geoffdavis/3DPrinterConfig/voronica/CANBUS/SB2040/H0a4bb9aa91b341e5a25d1acb4156db0cP.webp

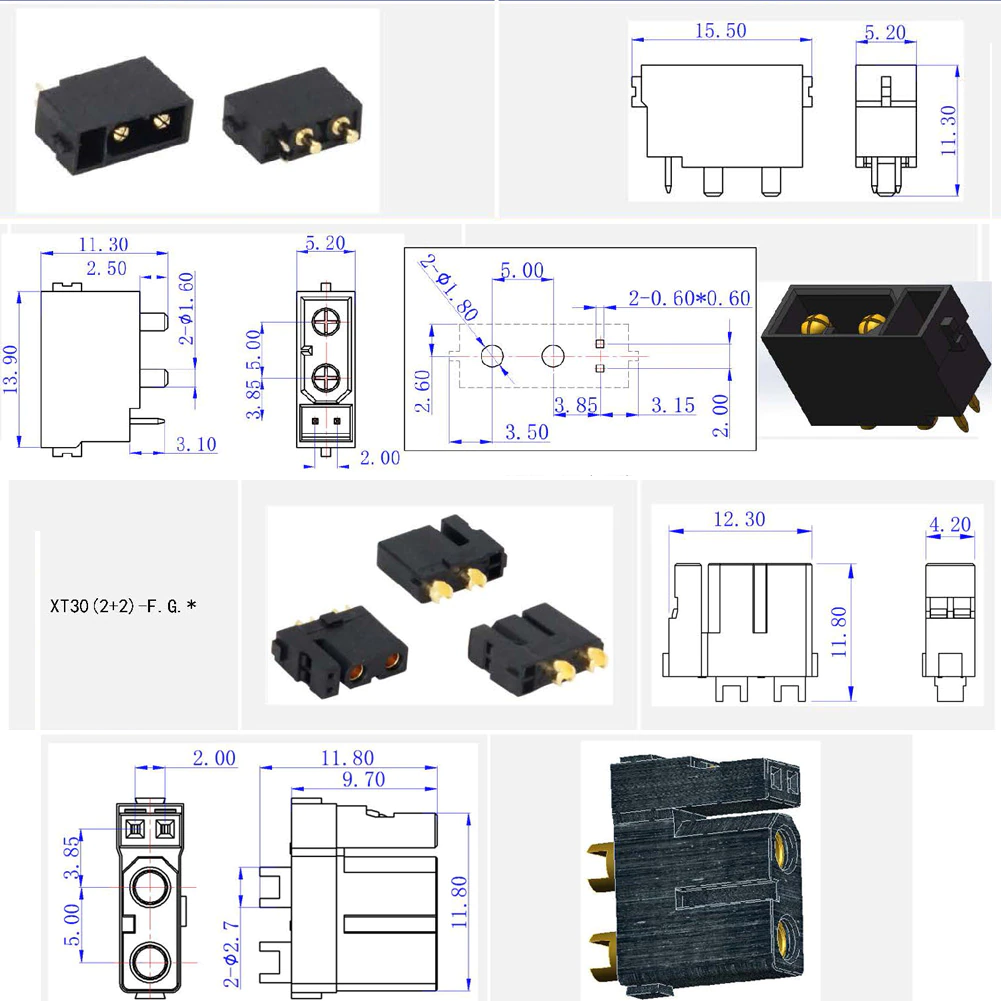
voronica/CANBUS/SB2040/H0a4bb9aa91b341e5a25d1acb4156db0cP.webp
