geoffdavis/3DPrinterConfig/voronica/CANBUS/SB2040/Hcbaf34d7871c420ca07bb667928e01d23.webp

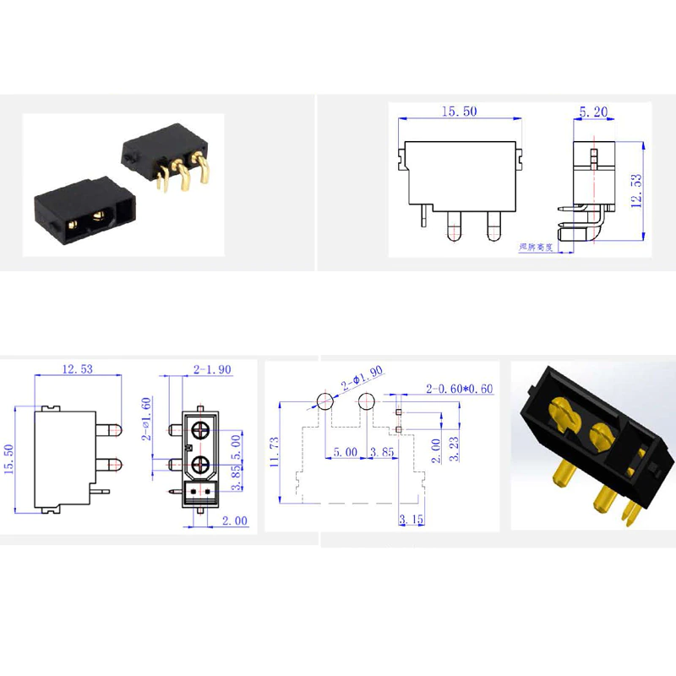
voronica/CANBUS/SB2040/Hcbaf34d7871c420ca07bb667928e01d23.webp
