geoffdavis/3DPrinterConfig/voronica/docs/Stepper Motors/Wiring_4_lead_Wires_c08b9b2bf8.png

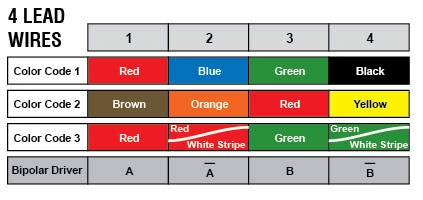
voronica/docs/Stepper Motors/Wiring_4_lead_Wires_c08b9b2bf8.png
