geoffdavis/3DPrinterConfig/smurf/klipper/printer.cfg

### UI
[include fluidd.cfg]

[mcu]
serial: /dev/serial0  # If you are using internal RPI serial port
# serial: /dev/ttyACM0 # If you are using RPI via USB connection to printer
restart_method: command

### CONTROL BOARD
[include config/boards/btt-skr-pico.cfg]

### RPI MCU
[include config/boards/rpi.cfg]

### Base Setup
[include config/printers/mpmd/mpmd.cfg]

### Stepper motors, drivers, & speed limits
[include config/printers/mpmd/steppers.cfg]

[include config/printers/mpmd/tmc2209.cfg]

[include config/printers/mpmd/speed-limits-basic.cfg]

# Stealth mode
# Note: this will make your printer quieter but less accurate, it's an inherent side effect of stealthchop
[include config/printers/mpmd/tmc2209-stealth.cfg]

### Homing
[include config/z-probe/probe.cfg]

#[include config/sensorless-homing.cfg]
[include config/printers/mpmd/endstops.cfg]

### Toolhead
# Extruder
[include config/extruders/cr10-clone.cfg]
[include config/sensors/btt-smartie.cfg]

# Hotend
[include config/hotends/revo.cfg]

### Macros
[include config/macros.cfg]
[include config/cancel-object.cfg]
[include config/chassis-neopixel.cfg]

[include config/beeper.cfg]

### SAVE VARIABLES
[save_variables]
filename: ~/klipper_config/saved_vars.cfg

### Local overrides

[printer]
#delta_radius: 62.7

[stepper_a]
#angle: 212.000000
#position_endstop: 120
#arm_length: 121.36

[stepper_b]
#angle: 330.000000
#position_endstop: 120
#arm_length: 121.36

[stepper_c]
#angle: 90.000000
#position_endstop: 120
#arm_length: 121.36

#[endstop_phase]

[probe]
#z_offset: -0.554

#*# <---------------------- SAVE_CONFIG ---------------------->
#*# DO NOT EDIT THIS BLOCK OR BELOW. The contents are auto-generated.
#*#
#*# [extruder]
#*# control = pid
#*# pid_kp = 29.404
#*# pid_ki = 3.770
#*# pid_kd = 57.337
#*#
#*# [probe]
#*# z_offset = -0.304
#*#
#*# [printer]
#*# delta_radius = 69.265389
#*#
#*# [stepper_a]
#*# angle = 208.082418
#*# arm_length = 129.677009
#*# position_endstop = 129.212455
#*#
#*# [stepper_b]
#*# angle = 329.908835
#*# arm_length = 134.705170
#*# position_endstop = 126.945224
#*#
#*# [stepper_c]
#*# angle = 90.000000
#*# arm_length = 131.403512
#*# position_endstop = 127.320085
#*#
#*# [delta_calibrate]
#*# height0 = 0.0
#*# height0_pos = 12766.000,12830.000,12696.000
#*# height1 = 0.0
#*# height1_pos = 15735.000,15881.000,10928.000
#*# height2 = 0.0
#*# height2_pos = 12413.000,17949.000,12333.000
#*# height3 = 0.0
#*# height3_pos = 11097.000,15438.000,15205.000
#*# height4 = 0.0
#*# height4_pos = 12305.000,12376.000,16029.000
#*# height5 = 0.0
#*# height5_pos = 14803.000,11220.000,14765.000
#*# height6 = 0.0
#*# height6_pos = 16615.000,12211.000,12109.000
#*# distance0 = 42.71
#*# distance0_pos1 = 12720.683,12836.172,12800.936
#*# distance0_pos2 = 11138.046,15373.365,15327.350
#*# distance1 = 42.51
#*# distance1_pos1 = 12813.143,12654.730,12892.586
#*# distance1_pos2 = 12453.914,12277.408,17382.719
#*# distance2 = 42.019999999999996
#*# distance2_pos1 = 12996.640,12564.830,12800.936
#*# distance2_pos2 = 15602.015,10997.053,15327.350
#*# distance3 = 42.52
#*# distance3_pos1 = 13087.652,12654.234,12619.827
#*# distance3_pos2 = 17680.406,12270.001,12239.706
#*# distance4 = 42.21
#*# distance4_pos1 = 12992.919,12835.668,12530.334
#*# distance4_pos2 = 15527.374,15363.343,10964.985
#*# distance5 = 43.43000000000001
#*# distance5_pos1 = 12809.483,12927.741,12619.827
#*# distance5_pos2 = 12399.234,17431.969,12239.706
#*# distance6 = 42.64
#*# distance6_pos1 = 11231.120,14818.516,15112.508
#*# distance6_pos2 = 12576.568,12137.110,17139.114
#*# distance7 = 42.25
#*# distance7_pos1 = 12553.959,12116.767,16675.793
#*# distance7_pos2 = 15645.929,11027.004,15025.022
#*# distance8 = 42.26
#*# distance8_pos1 = 15376.827,11087.549,14774.700
#*# distance8_pos2 = 17424.591,12391.071,12099.921
#*# distance9 = 42.44
#*# distance9_pos1 = 16945.852,12370.772,12079.853
#*# distance9_pos2 = 15219.829,15408.928,10995.112
#*# distance10 = 42.589999999999996
#*# distance10_pos1 = 14967.704,15148.609,11055.574
#*# distance10_pos2 = 12259.859,17187.540,12360.610
#*# distance11 = 42.730000000000004
#*# distance11_pos1 = 12241.335,16722.072,12340.098
#*# distance11_pos2 = 11170.063,15069.973,15372.496
