geoffdavis/3DPrinterConfig/voronica/klipper/trad_rack/trad_rack_btt_skr_mini_e3_v2.cfg

[mcu tr]
serial: /dev/serial/by-id/usb-Klipper_stm32f103xe_30FFDA054E4E353717730551-if00
restart_method: command

[temperature_sensor TradRack]
sensor_type: temperature_mcu
sensor_mcu: tr
min_temp: 0
max_temp: 125

[trad_rack]
selector_max_velocity: 400
selector_max_accel: 10000
toolhead_fil_sensor_pin: ^!sb2040:gpio29
lane_count: 14
lane_spacing: 17.0
servo_down_angle: 0.0
servo_up_angle: 131.0
toolhead_unload_speed: 20
extruder_load_speed: 20
toolhead_sense_speed: 20
selector_unload_length: 17.5
bowden_length: 950.0
extruder_load_length: 44.5
hotend_load_length: 6.0
toolhead_unload_length: 40.0
buffer_pull_speed: 200.0    # increase this to 300+ once you are ready
                            # (but some motors may not be able to handle this).
sync_to_extruder: true

[stepper_tr_selector]
# connected to XM
step_pin: tr:PB13
dir_pin: !tr:PB12
enable_pin: !tr:PB14
rotation_distance: 40
microsteps: 16
full_steps_per_rotation: 200
endstop_pin: ^tr:PC0 # X-STOP
position_min: 0.0
position_endstop: 0.0
position_max: 221   # (lane_count - 1) * lane_spacing
homing_speed: 30

[stepper_tr_fil_driver]
# connected to EM
step_pin: tr:PB3
dir_pin: !tr:PB4
enable_pin: !tr:PD2
rotation_distance: 22.67895
gear_ratio: 50:17
microsteps: 16
full_steps_per_rotation: 200
endstop_pin: ^tr:PC2  # selector filament sensor, Z-STOP
position_min: -5000
position_endstop: 0
position_max: 5000
homing_positive_dir: False

[tmc2209 stepper_tr_selector]
# connected to XM
uart_pin: tr:MMU_TMC_UART
tx_pin: tr:PC10
uart_address: 0
interpolate: True
run_current: 0.63   # for a 1A peak motor
sense_resistor: 0.110

[tmc2209 stepper_tr_fil_driver]
# connected to EM
uart_pin: tr:MMU_TMC_UART
tx_pin: tr:PC10
uart_address: 3
interpolate: False
run_current: 1.27   # for a 2A peak motor
sense_resistor: 0.110

[servo tr_servo]
# connected to servo/bltouch control pin
pin: tr:PA1
maximum_servo_angle: 131
minimum_pulse_width: 0.000700
maximum_pulse_width: 0.002200

[extruder]
max_extrude_only_distance: 200
max_extrude_cross_section: 100

# Macros
[gcode_macro ACTIVATE_EXTRUDER]
rename_existing: ACTIVATE_EXTRUDER.1
gcode:
    {% set EXTRUDER = params.EXTRUDER|default('extruder')|lower|replace('extruder', '') %}
    {% if EXTRUDER == '' %}
        {% set EXTRUDER = '0' %}
    {% endif %}
    TR_LOAD_TOOLHEAD LANE={EXTRUDER}
