geoffdavis/3DPrinterConfig/hodad/klipper/config/beeper.cfg

#####################################################################
#	Tones
# 
#     |~~~~~~~~~~~~~~~|
#     |~~~~~~~~~~~~~~~|
#     |               |
# /~~\|           /~~\|
# \__/            \__/
# 
#####################################################################

# Source: https://github.com/majarspeed/Profiles-Gcode-Macros/blob/main/Beeper%20tunes/tones.cfg

[gcode_macro TOGGLE_BEEPER]
description: Toggle the printer beeper on and off.
gcode:
	{% set beeper_state = printer.save_variables.variables.beeper_state|lower %}

	{% if printer['gcode_macro _USER_VARIABLE'].debug == 1 %}
		{action_respond_info('==== TOGGLE_BEEPER ====')}
		{action_respond_info("beeper_state: %s" % (beeper_state))}
		{action_respond_info('===============')}
	{% endif %}

	{% if beeper_state == "off" %}
		{action_respond_info('beeper is off, turning it on')}
		SAVE_VARIABLE VARIABLE=beeper_state VALUE='"on"'
	{% else %}
		{action_respond_info('beeper is on= turning it off')}
		SAVE_VARIABLE VARIABLE=beeper_state VALUE='"off"'
	{% endif %}
	SONG_SINGLE_BEEP

[gcode_macro SONG_SINGLE_BEEP]
gcode:
	M300 S830.61 P137

[gcode_macro BEEP]
gcode:
    # Parameters
    {% set i = params.I|default(1)|int %}           ; Iterations (number of times to beep).
    {% set dur = params.DUR|default(100)|int %}     ; Duration/wait of each beep in ms. Default 100ms.
    {% set freq = params.FREQ|default(2000)|int%}   ; Frequency in Hz. Default 2kHz.

    {% for iteration in range(1|int) %}
        SET_PIN PIN=beeper VALUE=0.8 CYCLE_TIME={ 1.0/freq if freq >0 else 1 }
        G4 P{dur}
        SET_PIN PIN=beeper VALUE=0
        G4 P{dur}
    {% endfor %}

[gcode_macro M300]
gcode:
	{% set S = params.S|default(1000)|int %}
	{% set P = params.P|default(100)|int %}

		SET_PIN PIN=beeper VALUE=0.5 CYCLE_TIME={ 1.0/S if S > 0 else 1 }
		G4 P{P}
		SET_PIN PIN=beeper VALUE=0

[gcode_macro SONG_THUNDERSTRUCK]
gcode:
	M300 S987 P166
	M300 S2489 P166
	M300 S987 P166
	M300 S2959 P166
	M300 S987 P166
	M300 S2489 P166
	M300 S987 P166
	M300 S2959 P166
	M300 S987 P166
	M300 S2489 P166
	M300 S987 P166
	M300 S2959 P166
	M300 S987 P166
	M300 S2959 P166
	M300 S987 P166
	M300 S2959 P166
	M300 S2637 P166
	M300 S987 P166
	M300 S1760 P166
	M300 S987 P166
	M300 S2637 P166
	M300 S987 P166
	M300 S1760 P166
	M300 S987 P166
	M300 S2637 P166
	M300 S987 P166
	M300 S1760 P166
	M300 S987 P166
	M300 S2637 P166
	M300 S987 P166
	M300 S1760 P166

[gcode_macro SONG_AFRICA]
gcode:
	M300 S2959 P150
	M300 S2959 P150
	M300 S2959 P150
	M300 S2959 P450
	M300 S2959 P150
	M300 S2959 P450
	M300 S3322 P300
	M300 S1864 P150
	M300 S1975 P1200
	M300 S2489 P150
	M300 S2489 P450
	M300 S2637 P300
	M300 S2959 P300
	M300 S2959 P300
	M300 S2637 P225
	M300 S2637 P300
	M300 S2489 P300
	M300 S2217 P600
	M300 S2217 P300
	M300 S987 P300
	M300 S2489 P600
	M300 S2217 P150
	M300 S987 P300
	M300 S2217 P1200
	M300 S2959 P150
	M300 S2959 P150
	M300 S2959 P600
	M300 S2959 P150
	M300 S2959 P450
	M300 S3322 P300
	M300 S1864 P150
	M300 S1975 P1200
	M300 S2489 P150
	M300 S2489 P150
	M300 S2489 P150
	M300 S2637 P300
	M300 S2959 P300
	M300 S2959 P450
	M300 S2637 P300
	M300 S2637 P300
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

[gcode_macro SONG_STARWARS_IMP]
gcode:
	M300 S1174 P401
	M300 S1174 P401
	M300 S1174 P401
	M300 S466 P267
	M300 S1396 P133
	M300 S1174 P401
	M300 S466 P267
	M300 S1396 P133
	M300 S1174 P803

[gcode_macro SONG_ALLIWANT]
gcode:
	M300 S1046 P333
	M300 S1318 P333
	M300 S1567 P333
	M300 S987 P166
	M300 S0 P41
	M300 S2093 P333
	M300 S0 P83
	M300 S0 P41
	M300 S987 P333
	M300 S880 P166
	M300 S0 P41
	M300 S1567 P333
	M300 S0 P83
	M300 S0 P41
	M300 S2349 P333
	M300 S2093 P333
	M300 S2093 P333
	M300 S987 P333
	M300 S2093 P166
	M300 S0 P41
	M300 S987 P333
	M300 S0 P83
	M300 S0 P41
	M300 S880 P166
	M300 S1567 P333
	M300 S0 P166
	M300 S1396 P333
	M300 S880 P333
	M300 S2093 P333
	M300 S2349 P333
	M300 S2637 P333
	M300 S2349 P166
	M300 S2093 P333
	M300 S880 P333
	M300 S0 P166
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
	M300 P249 S262
	M300 P249 S784
	M300 P247 S698
	M300 P247 S659
	M300 P250 S587
	M300 P265 S587
	M300 P248 S659
	M300 P247 S698
	M300 P249 S262
	M300 P249 S698
	M300 P247 S262
	M300 P247 S784
	M300 P250 S880
	M300 P265 S932
	M300 P248 S932
	M300 P247 S880
	M300 P249 S349
	M300 P249 S784
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
