geoffdavis/3DPrinterConfig/voronica/klipper/macros/start_stop.cfg

; Start/stop macros
; Uses heatsoak.cfg

[gcode_macro _START_STOP_VARS]
variable_trad_rack_present: 1
gcode:

[gcode_macro PRINT_START]
gcode:
    # Parameters
    {% set bedtemp = params.BED|default(60)|int %}
    {% set hotendtemp = params.HOTEND|default(215)|int %}
    {% set chambertemp = params.CHAMBER|default(0)|int %}
    {% set force_bedmesh = params.BEDMESH|default(1)|int %}
    {% set force_qgl = params.FORCE_QGL|default(1)|int %}


    {% set COLORS = params.COLORS|default("")|string %}
    {% set colors = COLORS.split(",") %}
    {% set ttg_map = printer.mmu.ttg_map %}

    #SET_FILAMENT_SENSOR SENSOR=btt_smartie ENABLE=0                          ; disable filament sensor

    {% if printer["temperature_sensor chamber"].temperature < chambertemp %}
      RESPOND MSG="Chamber Heating"
		  _HEATSOAK TEMP={bedtemp} MOVE=1                    # Set up to heat soak if chamber temp is set higher than current reading
		  M190 S{bedtemp}                                    # Set target bed temp & wait for it
      RESPOND MSG="Waiting for Chamber Temperature to reach {chambertemp}C"
      TEMPERATURE_WAIT SENSOR="temperature_sensor chamber" MINIMUM={chambertemp}   # Do the actual heat soak wait, until chamber temp is at target
      RESPOND MSG="Chamber Temperature reached {chambertemp}C"
    {% else %}
      RESPOND MSG="Bed Heating"
        {% if printer.heater_bed.temperature < (bedtemp-2) %}
          _HEATSOAK TEMP={bedtemp} MOVE=1	        	 # Bed is below target temp, get it heating & safely park toolhead
          M190 S{bedtemp}                                # Set bed target temp & wait for it
        {% else %}
          _HEATSOAK TEMP={bedtemp} MOVE=0                # Just do a bed heat, no champer temp (open case for PLA)
        {% endif %}
    {% endif %}
    M106 S0                                                  # Turn off part cooling fan from heatsoak

    # Conditionally re-mesh the bed
    {% if force_gql or not printer.quad_gantry_level.applied %}
      RESPOND MSG="Running Z-Gantry Leveling and Bed Meshing"
      led_meshing
      BED_MESH_CLEAR                                           # Clear old bed mesh  
      CALIBRATE_Z
      BED_MESH_CALIBRATE ADAPTIVE=1 ADAPTIVE_MARGIN=5
      LED_STANDBY
    {% elif force_bedmesh %}
      RESPOND MSG="Running Bed Meshing"
      led_meshing
      BED_MESH_CLEAR  
      BED_MESH_CALIBRATE ADAPTIVE=1 ADAPTIVE_MARGIN=5
      LED_STANDBY
    {% else %}
      RESPOND MSG="Skipping Bed Meshing"
      G28 ; Home all axes
    {% endif %}

    LED_HEATING
    #G1 X175 Y0 Z20         # Move tool head to safe distance from bed

    RESPOND MSG="Heating nozzle"
    M106 S205 ; set fan speed
    M109 S{hotendtemp}                                       # Do final nozzle heat
 
    LED_PRINTING                                             # Prep done, start print
    RESPOND MSG="Printing"
    SONG_SINGLE_BEEP

    #VORON_PURGE
    G90                            ; absolute positioning
    G1 Z20 F3000                   ; move nozzle away from bed 

#   Use PRINT_END for the slicer ending script - please customise for your slicer of choice
[gcode_macro PRINT_END]
gcode:
  {% set xy_offset = 20 %}
  {% set filter_off = 300 %}
  {% set retract_dist = 1800 %}
  {% set travel = 20000 %}
  {% set filter_off = 300 %}
  # calculate safe move
  {% set max = printer.toolhead.axis_maximum %}
  {% set act = printer.toolhead.position %}
  {% set safe = {'x': 20.0 if act.x|float < (max.x|float - 20.0) else -20.0,
                 'y': 20.0 if act.y|float < (max.y|float - 20.0) else -20.0,
                 'z':  2.0 if act.z|float < (max.z|float -  2.0) else (max.z|float - act.z|float)} %}
  
  M400                           ; wait for buffer to clear
  #SET_FILAMENT_SENSOR SENSOR=btt_smartie ENABLE=0                          ; disable filament sensor
  {% if printer.mmu is not defined or ( printer.mmu is defined and printer.mmu.enabled ) %}
  G92 E0                         ; zero the extruder
  G1 E-5 F{retract_dist}                ; retract filament
  G91                            ; relative positioning
  G0 Z1.00 X{safe.x} Y{safe.y} Z{safe.z} F{travel}    ; move nozzle to remove stringing
  {% endif %}

  TURN_OFF_HEATERS
  M107                           ; turn off fan
  G90                            ; absolute positioning
  PARKREAR            ; park nozzle at rear
  UPDATE_DELAYED_GCODE ID=_DELAY_FILTER_OFF DURATION={filter_off}
  ;BED_MESH_CLEAR
  ;Song_Simpsons
  M117 Print Complete!
  UPDATE_DELAYED_GCODE ID=clear_display DURATION=10
  LED_STANDBY
  M220 S100 ; set feedrate percentage back to default
  M221 S100 ; set speed percentage back to default
