geoffdavis/3DPrinterConfig/voronica/klipper/pause_resume.cfg

# Pause / Resume
# https://ellis3dp.com/Print-Tuning-Guide/articles/useful_macros/pause_resume_filament.html


# Declare the pause_resume feature
[pause_resume]

[gcode_macro PAUSE_RESUME_VARS]
variable_manage_sensor: 0 ; set this to 0 if btt-smartie is commented out
variable_sensor_name: "btt_smartie"
gcode:

[gcode_macro PAUSE]
rename_existing: BASE_PAUSE
gcode:
    # Parameters
    {% set z = params.Z|default(10)|int %}                                               ; z hop amount

    {% if printer['pause_resume'].is_paused|int == 0 %}
        SET_GCODE_VARIABLE MACRO=RESUME VARIABLE=zhop VALUE={z}                              ; set z hop variable for reference in resume macro
        SET_GCODE_VARIABLE MACRO=RESUME VARIABLE=etemp VALUE={printer['extruder'].target}    ; set hotend temp variable for reference in resume macro

        {% if printer['gcode_macro PAUSE_RESUME_VARS'].manage_sensor > 0 %}
        SET_FILAMENT_SENSOR SENSOR={printer['gcode_macro PAUSE_RESUME_VARS'].sensor_name} ENABLE=0                                  ; disable filament sensor
        {% endif %}
        SAVE_GCODE_STATE NAME=PAUSE                                                          ; save current print position for resume
        LED_STANDBY                                                                          ; Set lights for standby mode
        BASE_PAUSE                                                                           ; pause print
        {% if (printer.gcode_move.position.z + z) < printer.toolhead.axis_maximum.z %}       ; check that zhop doesn't exceed z max
            G91                                                                              ; relative positioning
            G1 Z{z} F900                                                                     ; raise Z up by z hop amount
        {% else %}
            { action_respond_info("Pause zhop exceeds maximum Z height.") }                  ; if z max is exceeded, show message and set zhop value for resume to 0
            SET_GCODE_VARIABLE MACRO=RESUME VARIABLE=zhop VALUE=0
        {% endif %}
        G90                                                                                  ; absolute positioning
        G1 X{printer.toolhead.axis_maximum.x/2} Y{printer.toolhead.axis_minimum.y+5} F6000   ; park toolhead at front center
        SAVE_GCODE_STATE NAME=PAUSEPARK                                                      ; save parked position in case toolhead is moved during the pause (otherwise the return zhop can error)
        ;M104 S0                                                                              ; turn off hotend (disabled because it breaks tradrack)
        SET_IDLE_TIMEOUT TIMEOUT=43200                                                       ; set timeout to 12 hours
    {% endif %}

[gcode_macro RESUME]
rename_existing: BASE_RESUME
variable_zhop: 0
variable_etemp: 0
gcode:
    # Parameters
    {% set e = params.E|default(2.5)|int %}                                          ; hotend prime amount (in mm)

    {% if printer['pause_resume'].is_paused|int == 1 %}
        
        {% if printer['gcode_macro PAUSE_RESUME_VARS'].manage_sensor > 0 %}
        SET_FILAMENT_SENSOR SENSOR={printer['gcode_macro PAUSE_RESUME_VARS'].sensor_name} ENABLE=1                          ; enable filament sensor
        {% endif %}
        LED_PRINTING                                                                    ; reset LCD color
        SET_IDLE_TIMEOUT TIMEOUT={printer.configfile.settings.idle_timeout.timeout}  ; set timeout back to configured value
        {% if etemp > 0 %}
            M109 S{etemp|int}                                                        ; wait for hotend to heat back up
        {% endif %}
        RESTORE_GCODE_STATE NAME=PAUSEPARK MOVE=1 MOVE_SPEED=100                     ; go back to parked position in case toolhead was moved during pause (otherwise the return zhop can error)
        G91                                                                          ; relative positioning
        M83                                                                          ; relative extruder positioning
        {% if printer[printer.toolhead.extruder].temperature >= printer.configfile.settings.extruder.min_extrude_temp %}
            G1 Z{zhop * -1} E{e} F900                                                ; prime nozzle by E, lower Z back down
        {% else %}
            G1 Z{zhop * -1} F900                                                     ; lower Z back down without priming (just in case we are testing the macro with cold hotend)
        {% endif %}
        RESTORE_GCODE_STATE NAME=PAUSE MOVE=1 MOVE_SPEED=60                          ; restore position
        BASE_RESUME                                                                  ; resume print
    {% endif %}

[gcode_macro CANCEL_PRINT]
rename_existing: BASE_CANCEL_PRINT
gcode:
    SET_IDLE_TIMEOUT TIMEOUT={printer.configfile.settings.idle_timeout.timeout} ; set timeout back to configured value
    CLEAR_PAUSE
    SDCARD_RESET_FILE
    PRINT_END
    BASE_CANCEL_PRINT

[delayed_gcode DISABLEFILAMENTSENSOR]
initial_duration: 1
gcode:
    {% if printer['gcode_macro PAUSE_RESUME_VARS'].manage_sensor > 0 %} 
    SET_FILAMENT_SENSOR SENSOR={printer['gcode_macro PAUSE_RESUME_VARS'].sensor_name} ENABLE=0
    {% endif %}
