geoffdavis/3DPrinterConfig/voronica/klipper/fluidd.cfg

[virtual_sdcard]
path: /home/pi/printer_data/gcodes

[pause_resume]

[display_status]

[gcode_macro CANCEL_PRINT]
description: Cancel the actual running print
rename_existing: CANCEL_PRINT_BASE
gcode:
    TURN_OFF_HEATERS
    CANCEL_PRINT_BASE

# See macros/pause_resume.cfg for PAUSE and RESUME macros
