geoffdavis/3DPrinterConfig/voronica/klipper/macros/M141.cfg

# Set exhaust fan temperature target
[gcode_macro M141]
gcode:
    #SET_TEMPERATURE_FAN_TARGET TEMPERATURE_FAN=exhaust_fan TARGET={params.S}
    RESPOND MSG="M141: exhaust fan is a heater_fan, no direct control available"
