geoffdavis/3DPrinterConfig/voronica/klipper/probe.cfg

#####################################################################
#   Probe
#####################################################################

##  This probe is not used for Z height, only Quad Gantry Leveling
##  In Z+ position
[probe]
##  If your probe is NO instead of NC, change pin to ^!PA3
#pin: ^Z_MIN
pin: !sb2040:gpio28
x_offset: 0
#y_offset: 25.0 # physical probe
y_offset: 0 # TAP
#z_offset: -1.000
speed: 10.0
samples: 3
samples_result: median
sample_retract_dist: 3.0
samples_tolerance: 0.006
samples_tolerance_retries: 3

activate_gcode:
    {% set PROBE_TEMP = 170 %}
    {% set MAX_TEMP = PROBE_TEMP + 5 %}
    {% set ACTUAL_TEMP = printer.extruder.temperature %}
    {% set TARGET_TEMP = printer.extruder.target %}

    {% if TARGET_TEMP > PROBE_TEMP %}
        { action_respond_info('Extruder temperature target of %.1fC is too high, lowering to %.1fC' % (TARGET_TEMP, PROBE_TEMP)) }
        M109 S{ PROBE_TEMP }
    {% else %}
        # Temperature target is already low enough, but nozzle may still be too hot.
        {% if ACTUAL_TEMP > MAX_TEMP %}
            { action_respond_info('Extruder temperature %.1fC is still too high, waiting until below %.1fC' % (ACTUAL_TEMP, MAX_TEMP)) }
            TEMPERATURE_WAIT SENSOR=extruder MAXIMUM={ MAX_TEMP }
        {% endif %}
    {% endif %}

[bed_mesh]
#speed: 300
speed: 1000
#horizontal_move_z: 10
horizontal_move_z: 3
mesh_min: 40, 40
mesh_max: 310,310
#fade_start: 0.6
fade_start: 0.8
fade_end: 10.0
probe_count: 5,5
algorithm: bicubic
#relative_reference_index: 12
zero_reference_position: 175.0, 175.0

##  Use QUAD_GANTRY_LEVEL to level a gantry.
##  Min & Max gantry corners - measure from nozzle at MIN (0,0) and 
##  MAX (250, 250), (300,300), or (350,350) depending on your printer size
##  to respective belt positions
[quad_gantry_level]

#--------------------------------------------------------------------
##  Gantry Corners for 250mm Build
##  Uncomment for 250mm build
#gantry_corners:
#   -60,-10
#   310, 320
##  Probe points
#points:
#   50,25
#   50,175
#   200,175
#   200,25
    
##  Gantry Corners for 300mm Build
##  Uncomment for 300mm build
#gantry_corners:
#   -60,-10
#   360,370
##  Probe points
#points:
#   50,25
#   50,225
#   250,225
#   250,25

##  Gantry Corners for 350mm Build
##  Uncomment for 350mm build
gantry_corners:
   -60,-10
   410,420
##  Probe points
points:
   50,25
   50,275
   300,275
   300,25

#--------------------------------------------------------------------
#speed: 150
speed: 1000
horizontal_move_z: 10
retries: 8
retry_tolerance: 0.0075
max_adjust: 10
