geoffdavis/3DPrinterConfig/voronica/klipper/macros/heatsoak.cfg

[gcode_macro _HEATSOAK]
description: Helper: Set up to heat soak printer. Usage: _HEATSOAK [TEMP=temp(110)] [MOVE=move(1)]
gcode:
    {% set temp = params.TEMP|default(110)|int %}
    {% set move = params.MOVE|default(1)|int %}
	
    LED_HEATING
    RESPOND MSG="Warming up"
	M141 S0                                                 # Turn off exhaust fan
	M140 S{temp}                                            # Heat the bed
  M104 S170                                               # Set hotend to no-ooze temp
	{% if temp >= 90 %}                                    # It's ABS or other high-temp plastic, closed case
		M106 S205                                             # Turn on part fan to 80% for 
		_FILTER_ON                                            # Turn on Nevermore fans to circulate & accelerate chamber soak
    _FILTER_INFO
	{% else %}
		M106 S0                                               # Turn off part fan. Open case, no need
		_SET_FILTER                                           # Make sure Nevermore is off
    _FILTER_INFO
	{% endif %}
	
	{% if move == 1 %}
		_CG28                                                 # Conditional home
		PARKCENTER                                            # Park toolhead in safe location (center volume)
		LED_HEATING
	{% endif %}
