geoffdavis/3DPrinterConfig/hodad/klipper/klipper-expander.cfg

[mcu expander]
serial: /dev/serial/by-id/usb-Klipper_stm32f042x6_08002300134330534E373720-if00
restart_method: command

[output_pin caselight]
pin: expander:PA0
pwm: true
shutdown_value: 0
value: 1
cycle_time: 0.01

[neopixel expander]
pin: expander:PB1
chain_count: 1
initial_RED: 0.9
initial_GREEN: 0.3
initial_BLUE: 0.0
