geoffdavis/3DPrinterConfig/hodad/klipper/V0Display.cfg

[mcu display]
serial: /dev/serial/by-id/usb-Klipper_stm32f042x6_05001A000643564E32313720-if00
restart_method: command

[display]
lcd_type: sh1106
i2c_mcu: display
i2c_bus: i2c1a
# Set the direction of the encoder wheel
#   Standard: Right (clockwise) scrolls down or increases values. Left (counter-clockwise scrolls up or decreases values.
encoder_pins: ^display:PA3, ^display:PA4
#   Reversed: Right (clockwise) scrolls up or decreases values. Left (counter-clockwise scrolls down or increases values.
#encoder_pins: ^display:PA4, ^display:PA3
click_pin: ^!display:PA1
kill_pin: ^!display:PA5
x_offset: 2
#   Use X offset to shift the display towards the right. Value can be 0 to 3
vcomh: 31
#   Set the Vcomh value on SSD1306/SH1106 displays. This value is
#   associated with a "smearing" effect on some OLED displays. The
#   value may range from 0 to 63. Default is 0.
#   Adjust this value if you get some vertical stripes on your display. (31 seems to be a good value)

[neopixel displayStatus]
pin: display:PA0
chain_count: 1
color_order: GRB
initial_RED: 0.2
initial_GREEN: 0.05
initial_BLUE: 0

[output_pin beeper]
pin: display:PA6 # gpio1
value: 0
shutdown_value: 0
pwm: True
cycle_time: 0.0005 ; Default beeper tone in kHz. 1 / 0.0005 = 2000Hz (2kHz)
