geoffdavis/3DPrinterConfig/voronica/klipper/macros/filter.cfg

[gcode_macro _SET_FILTER]
description: Helper: Set Nevermore filter speed
gcode: SET_FAN_SPEED FAN=filter SPEED={params.S|default(0)}

[gcode_macro _FILTER_ON]
description: Helper: Nevermore on
gcode: _SET_FILTER S=1
  
[gcode_macro FILTER]
description: Toggle Nevermore fan
gcode:
  {% if printer['fan_generic filter'].speed|float > 0.0 %} _SET_FILTER {% else %} _FILTER_ON {% endif %}
  _FILTER_INFO

[delayed_gcode _DELAY_FILTER_OFF]
gcode:
  {% if printer.print_stats.state|lower != "paused" and printer.print_stats.state|lower != "printing" %}
    _SET_FILTER
    _FILTER_INFO
  {% endif %}

[gcode_macro _FILTER_INFO]
description: Helper: Print Nevermore speed
gcode: {action_respond_info("Filter fan %s" % 'on' if printer['fan_generic filter'].speed|float > 0.0 else 'off')}
