geoffdavis/3DPrinterConfig/voronica/klipper/extruder/clockwork2.cfg

[extruder]
## On SB2040
step_pin: sb2040:gpio9
dir_pin: sb2040:gpio10
enable_pin: !sb2040:gpio7
max_extrude_only_distance: 101

##  Update value below when you perform extruder calibration
##  If you ask for 100mm of filament, but in reality it is 98mm:
##  rotation_distance = <previous_rotation_distance> * <actual_extrude_distance> / 100
##  22.6789511 is a good starting point for Bondtech 5mm gears
##  34.37086 for Bondtech 8mm gears (Galileo)
rotation_distance: 22.292634 # calibration 9 Jan 2023
##  Update Gear Ratio depending on your Extruder Type
##  Use 50:17 for Afterburner/Clockwork (BMG Gear Ratio)
##  Use 80:20 for M4, M3.1
##  Use 7.5:1 for Galileo
gear_ratio: 50:10               #SB Pancake
microsteps: 16 #32
full_steps_per_rotation: 200    #200 for 1.8 degree, 400 for 0.9 degree
nozzle_diameter: 0.400
filament_diameter: 1.75

##  In E0-MOT Position
##  Make sure to update below for your relevant driver (2208 or 2209)
[tmc2209 extruder]
#uart_pin: E0_CS
uart_pin: sb2040:gpio8
interpolate: false
run_current: 0.55 # 0.50
sense_resistor: 0.110
stealthchop_threshold: 0

[verify_heater extruder]
check_gain_time: 40
max_error: 500
