geoffdavis/3DPrinterConfig/voronica/klipper/macros/M900.cfg

[gcode_macro M900]
description: Set Pressure Advance
gcode:
  ;SET_PRESSURE_ADVANCE ADVANCE={params.K|default(0)}
