geoffdavis/3DPrinterConfig/voronica/klipper/macros/M600.cfg

[gcode_macro M600]
description: Pause for filament change
gcode:
    #LCDRGB R=0 G=1 B=0  ; Turn LCD green
    PAUSE                ; Pause
