geoffdavis/3DPrinterConfig/voronica/klipper/lighting/caselight.cfg

#####################################################################
#  Caselight pin Definition
#####################################################################
## Caseight - In RGB Header G Position
[output_pin caselight]
pin: LED_G
pwm: true
hardware_pwm: true
shutdown_value: 0.75
value: 0.75
cycle_time: 0.0001

#####################################################################
#  Macros
#####################################################################
[gcode_macro _CASELIGHT_ON]
description: Helper: Light on
gcode:
  SET_PIN PIN=caselight VALUE={printer['gcode_macro _USER_VARIABLE'].peripheral.caselight.on_val}
  {action_respond_info("Caselight on")}
    
[gcode_macro _CASELIGHT_OFF]
description: Helper: Light off
gcode:
  SET_PIN PIN=caselight VALUE=0.0
  {action_respond_info("Caselight off")}

[gcode_macro CASELIGHT]
description: Toggle light
gcode: {% if printer['output_pin caselight'].value == 0 %} _CASELIGHT_ON {% else %} _CASELIGHT_OFF {% endif %}
